visionspacetec/VST104/PSpiceModels/power_management.asc

C1: cap; 4700p
C2: cap
C3: cap
C4: cap; 1n
C5: cap
C6: cap; 4700p
C7: cap; 1n
C8: cap
C9: cap
C10: cap
CL1: cap; 100n
CL2: cap; 100n
D1: diode; CDBQR40
D2: diode; CDBQR40
D3: diode; CDBQR40
D4: diode; CDBQR40
EF1: TPS25940-Q1_TRANS
EF2: TPS25940-Q1_TRANS
LG1: SN74LVC1G11
Q1: TPS22965_TRANS
Q2: TPS22965_TRANS
R1: res; 210k
R2: res; 8.45k
R3: res; 48.7k
R4: res; 10k
R5: res; 75k
R6: res; 33.2k
R7: res; 110k
R8: res; 33.2k
R9: res
R10: res
R11: res; 75k
R12: res; 48.7k
R13: res; 8.45k
R14: res; 210k
R15: res; 33.2k
R16: res; 110k
R17: res; 100k
R18: res; 33.2k
R19: res; 10k
R20: res
R21: res
R22: res
RL1: res; 25
RL2: res; 25
U11: BZT52C3V3T
V1: voltage; 5
V2: voltage; 5
Named nets: 0, curr_3V3, out_3V3, curr_5V, out_5V, load_5V, load_3V3, enable, kill_switch
.MODEL CDBQR40 D (Vpk=40 Ipk=0.6 Iave=0.2 diss=0.125 Vfwd=1 Revilimit=0.2e-6 Fc=5e-12 Tt=5e-9)
