visionspacetec/VST104/SpiceSimulations/power_protection/power_protection.asc

C1: cap; 100p
C2: cap; 1n
C6: cap; 10µ
C8: cap; 10µ
C9: cap; 22µ
C10: cap; 10µ
C11: cap; 22µ
C12: cap; 10µ
D1: diode; 15zener
D2: diode; 15zener
D4: diode; 15zener
R1: res; 75k
R2: res; 10k
R3: res; 16k
R4: res; 20k
R5: res; 22k
R6: res; 100k
R7: res; 100k
R8: res; 22k
R9: res; 10
R10: res; 100k
R16: res; 100k
R17: res; 10
R18: res; 100k
R19: res; 100k
R23: res; 0
R24: res; 0
RL0: res; 10
RL1: res; 10
RL2: res; 10
U0: TL431LI_TRANS
U1: SQD40061EL
U2: SQD40061EL
U3: SQD40061EL
U4: 2N7002BK
U5: SQD40061EL
U6: SQD40061EL
U7: SQD40061EL
U8: SQD40061EL
U9: 2N7002BK
V1: voltage; PWL(0 7 200m 20)
V2: voltage; 5
Named nets: 0, LOAD0, LOAD1, LOAD2, V_USB
.tran 200m
.model 15zener D BV=15
