visionspacetec/VST104/SpiceSimulations/power_management/power_management.asc

C1: cap; 22n
C2: cap; 22µ
C3: cap; 100n
C4: cap; 1n
C5: cap; 2µ
C6: cap; 15n
C7: cap; 1n
C8: cap; 22µ
C9: cap; 100n
C10: cap; 2µ
CL1: cap; 100µ
CL2: cap; 100µ
D1: diode; CDBQR40
D2: diode; CDBQR40
D3: diode; CDBQR40
D4: diode; CDBQR40
R1: res; 210k
R2: res; 16.9k
R3: res; 86.6k
R4: res; 10k
R5: res; 75k
R6: res; 33.2k
R7: res; 110k
R8: res; 60.4k
R9: res; 8.1
R10: res; 8.1
R11: res; 75k
R12: res; 48.7k
R13: res; 6.49k
R14: res; 210k
R15: res; 33.2k
R16: res; 110k
R17: res; 100k
R18: res; 31.6k
R19: res; 10k
R20: res; 330
R21: res; 12
R22: res; 12
RL1: res; 25
RL2: res; 25
U1: TPS25940-Q1_TRANS
U2: TPS22965_TRANS
U3: TPS25940-Q1_TRANS
U4: TPS22965_TRANS
U6: SN74LVC1G11
V1: voltage; PWL(0 3.3 50m 3.3 50.1m 0)
V2: voltage; 5
V3: voltage; PWL(0 3.3 10m 3.3 10.1m 0 20m 3.3)
Named nets: 0, curr_3V3, out_3V3, curr_5V, out_5V, load_5V, load_3V3, enable, kill_switch
.MODEL CDBQR40 D (Vpk=40 Ipk=0.6 Iave=0.2 diss=0.125 Vfwd=1 Revilimit=0.2e-6 Fc=5e-12 Tt=5e-9)
.tran 100m
